onxblog/DSS/Complit_images/1.jpg

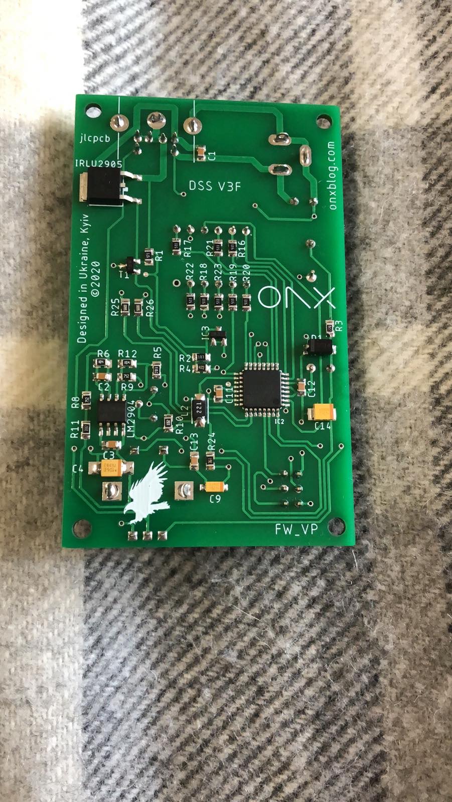
Complit_images/1.jpg
