onxblog/DSS/Complit_images/2.jpg

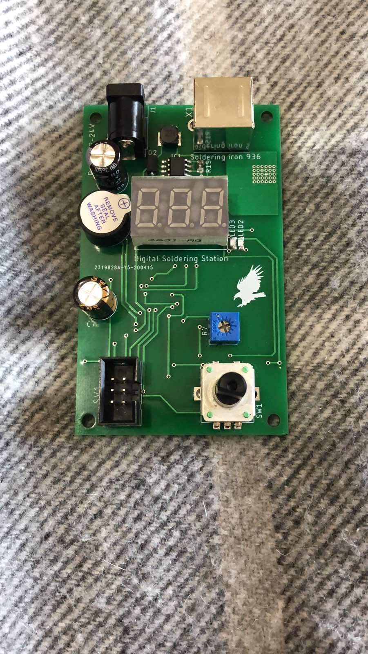
Complit_images/2.jpg
