onxblog/DSS/Complit_images/IMG_0458.jpg

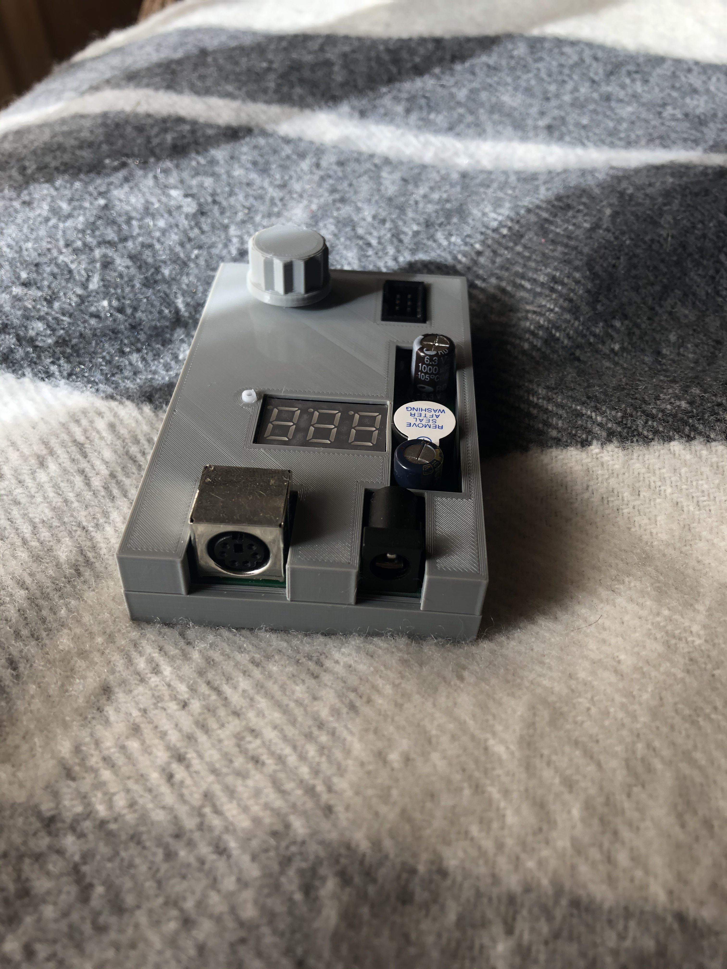
Complit_images/IMG_0458.jpg
