onxblog/DSS/Complit_images/IMG_0459.jpg

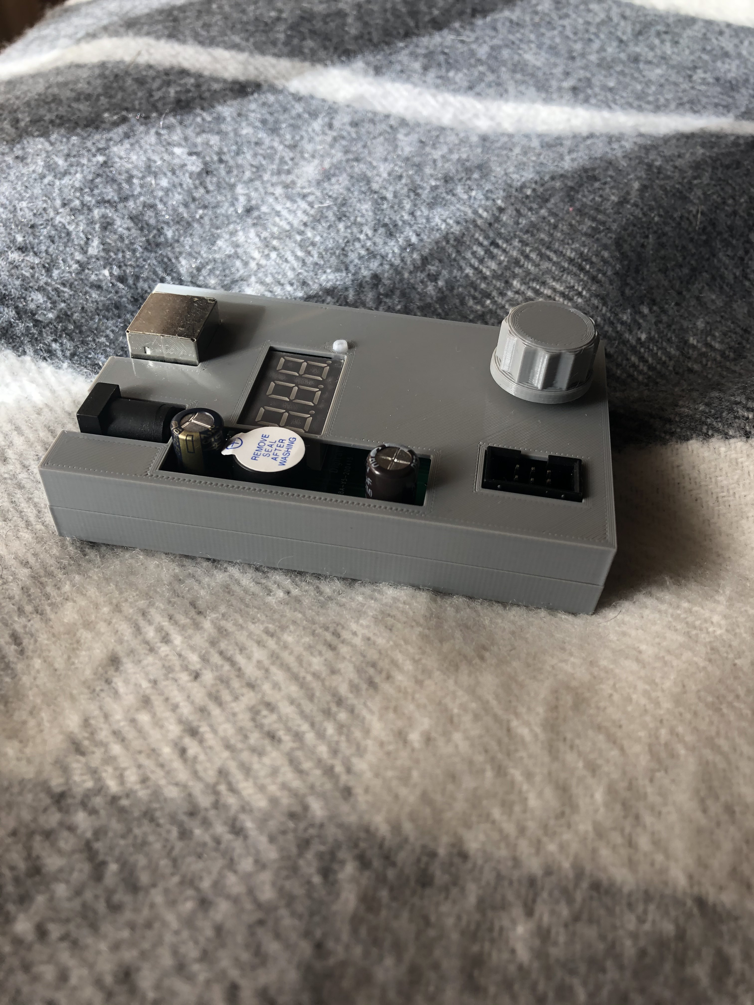
Complit_images/IMG_0459.jpg
