onxblog/DSS/Firmware_bin/fuses_1.jpg

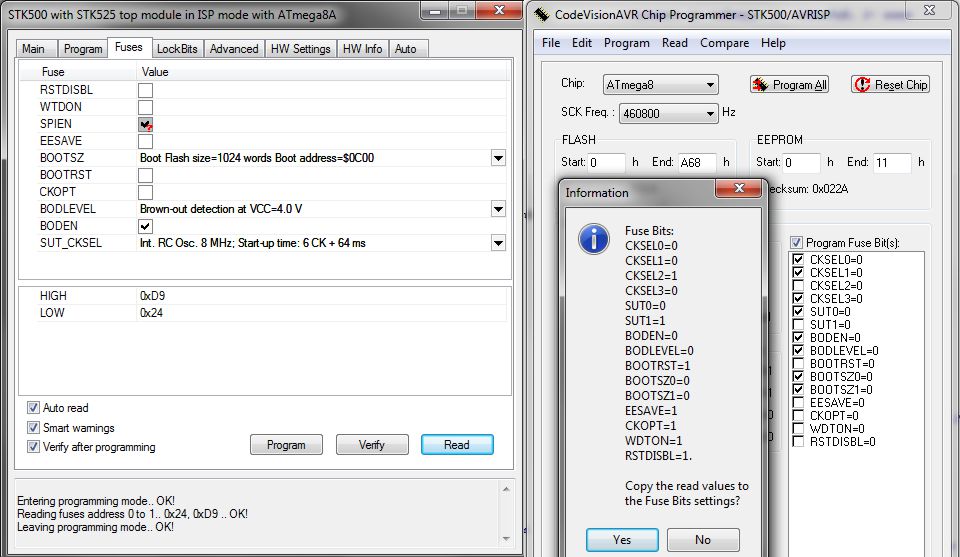
Firmware_bin/fuses_1.jpg
