onxblog/DSS/Complit_images/IMG_0457.jpg

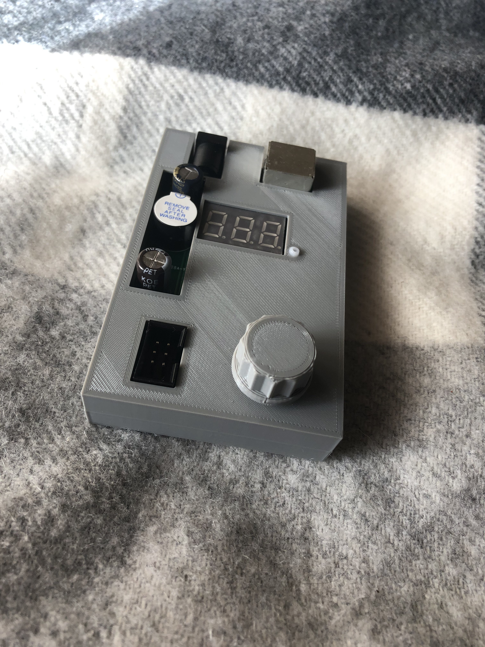
Complit_images/IMG_0457.jpg
